LowPowerLab/Moteino/R6/MoteinoR6_rendering.png

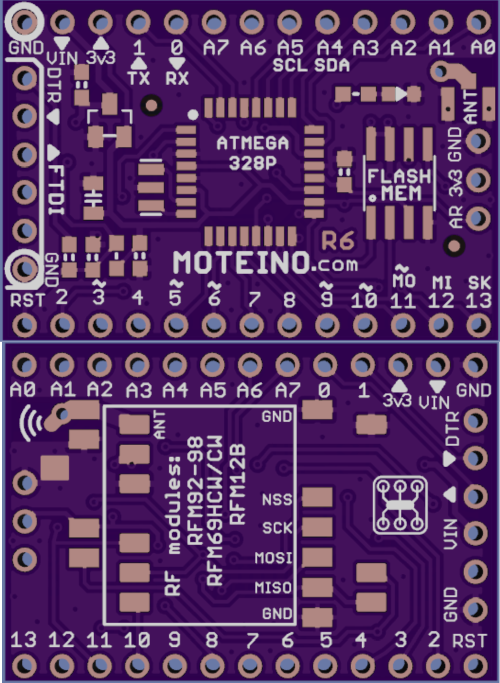
R6/MoteinoR6_rendering.png
