LowPowerLab/Moteino/DXF/Dimension-Moteino.png

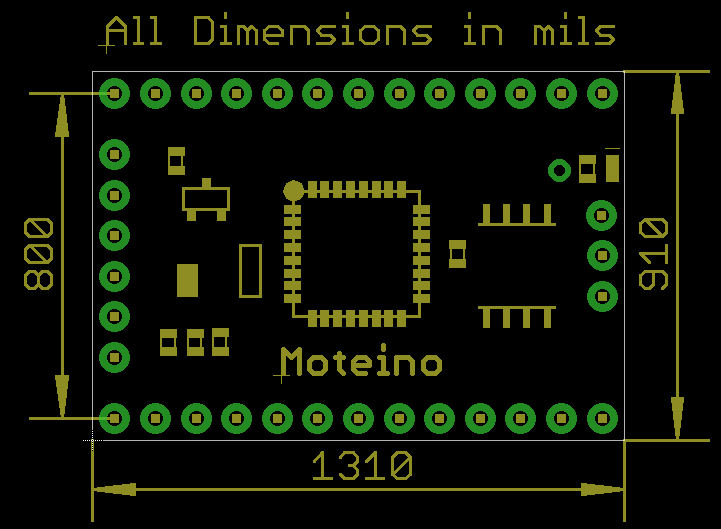
DXF/Dimension-Moteino.png
