LowPowerLab/Moteino/DXF/Dimension-MoteinoMEGA.png

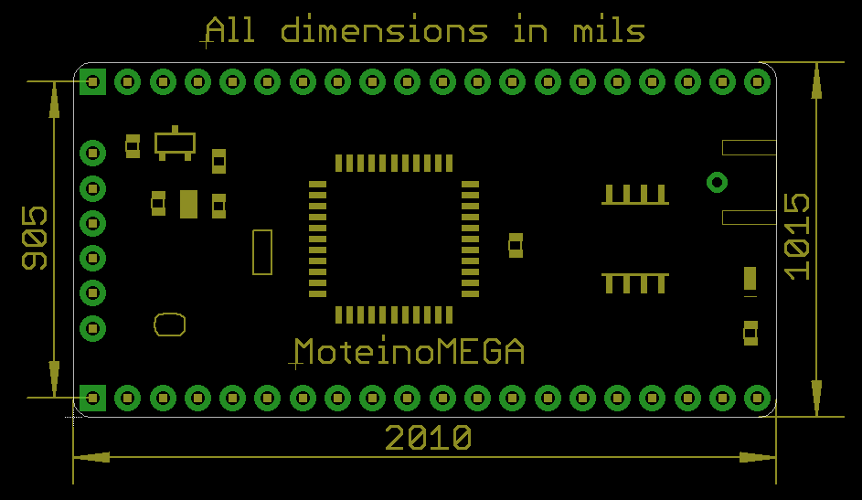
DXF/Dimension-MoteinoMEGA.png
