LowPowerLab/Moteino/DXF/Dimension-MoteinoUSB.png

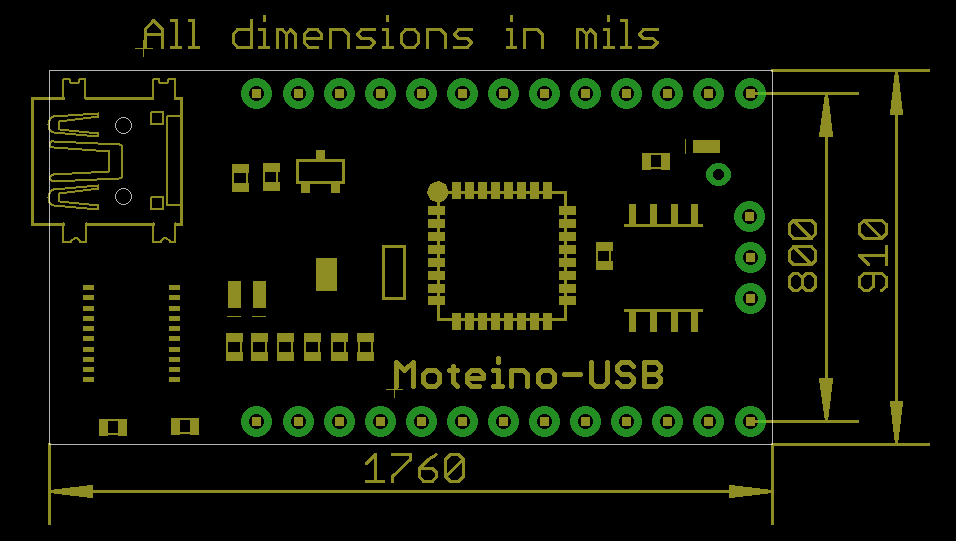
DXF/Dimension-MoteinoUSB.png
