LowPowerLab/Moteino/R4/MoteinoR4_STENCIL.png

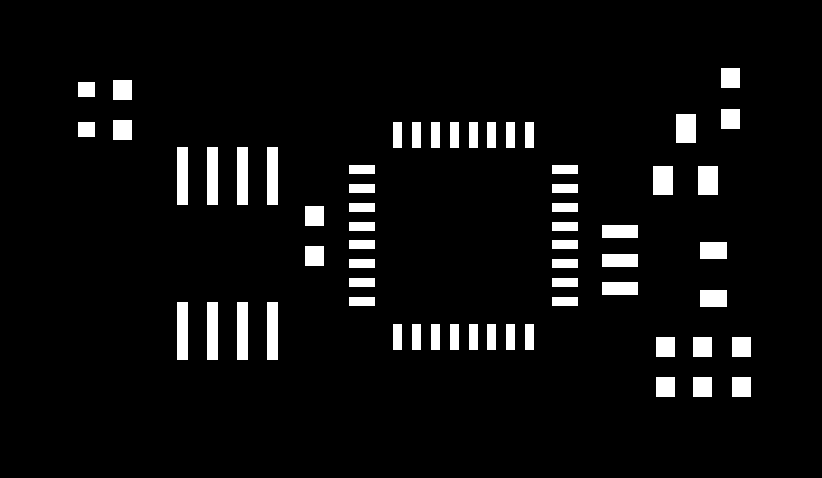
R4/MoteinoR4_STENCIL.png
