LowPowerLab/Moteino/R4/MoteinoR4LR_BRD_BOTTOM.png

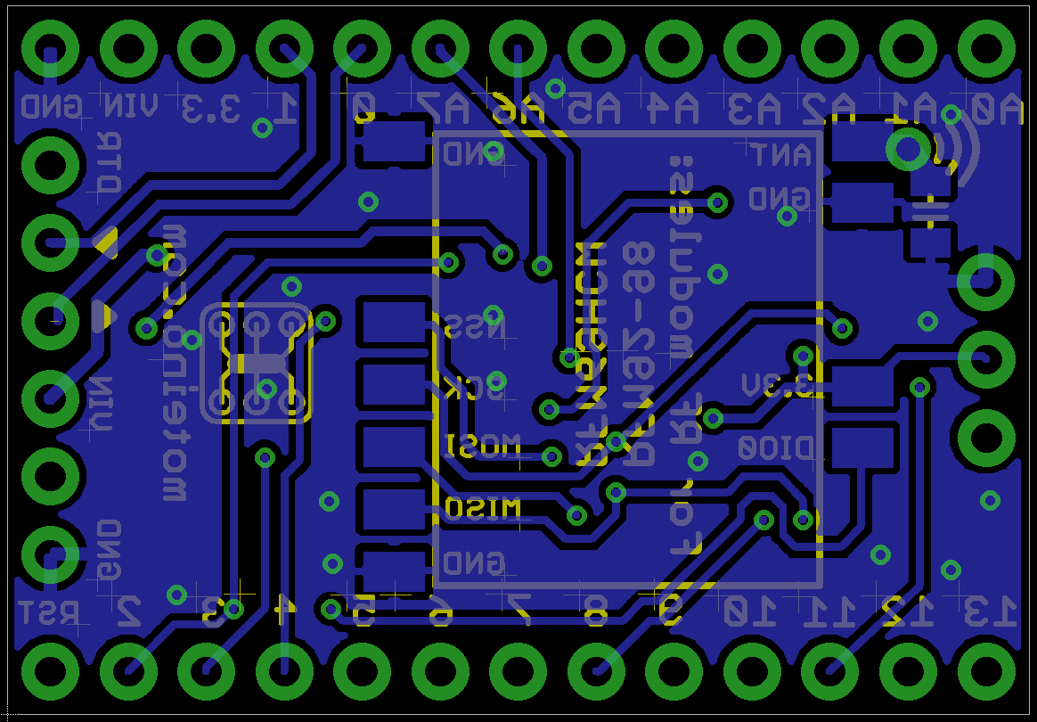
R4/MoteinoR4LR_BRD_BOTTOM.png
