LowPowerLab/Moteino/R4/Rendering_bottom.png

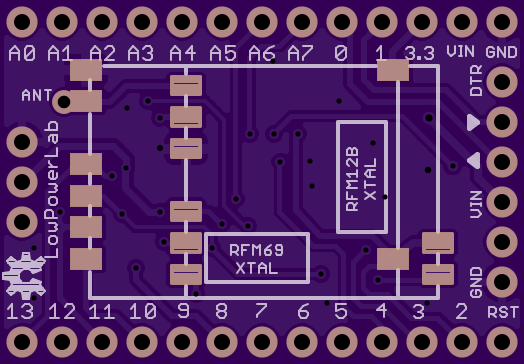
R4/Rendering_bottom.png
