LowPowerLab/Moteino/R4/Rendering_top.png

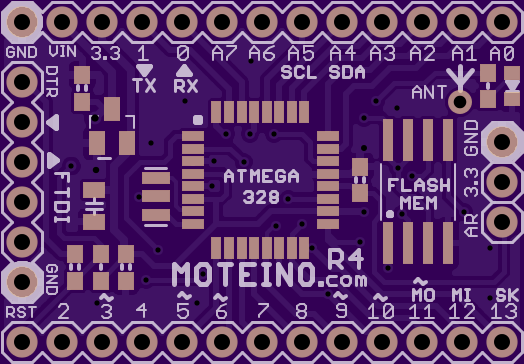
R4/Rendering_top.png
