LowPowerLab/Moteino/R4USB/MoteinoR4_USB_STENCIL.png

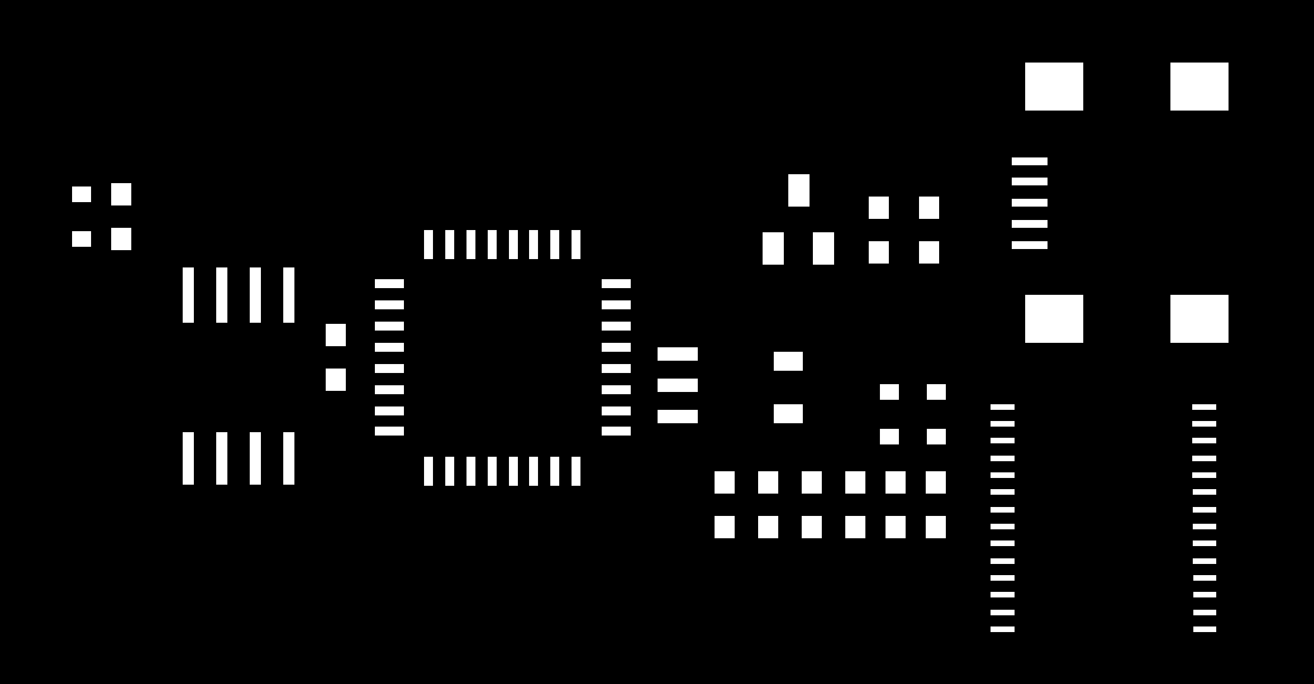
R4USB/MoteinoR4_USB_STENCIL.png
