LowPowerLab/Moteino/R4USB/Rendering_bottom.png

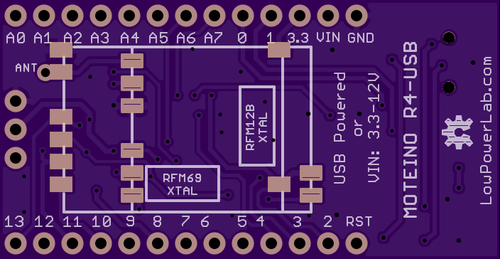
R4USB/Rendering_bottom.png
