LowPowerLab/Moteino/R5USB/MoteinoR5USB_dimension.png

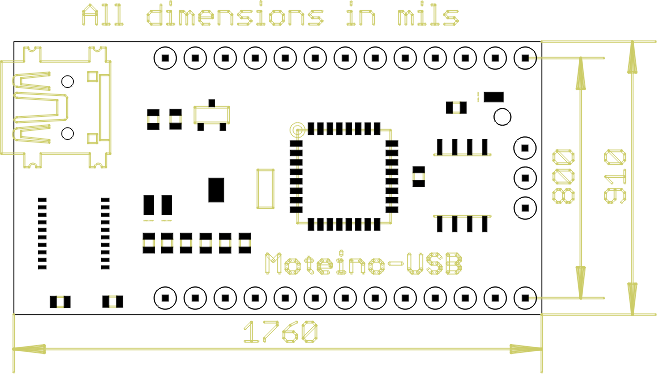
R5USB/MoteinoR5USB_dimension.png
